Obrelix/Arduino-Granular-Synth-Theremin-v2/Images/IMG_20230304_175001.jpg

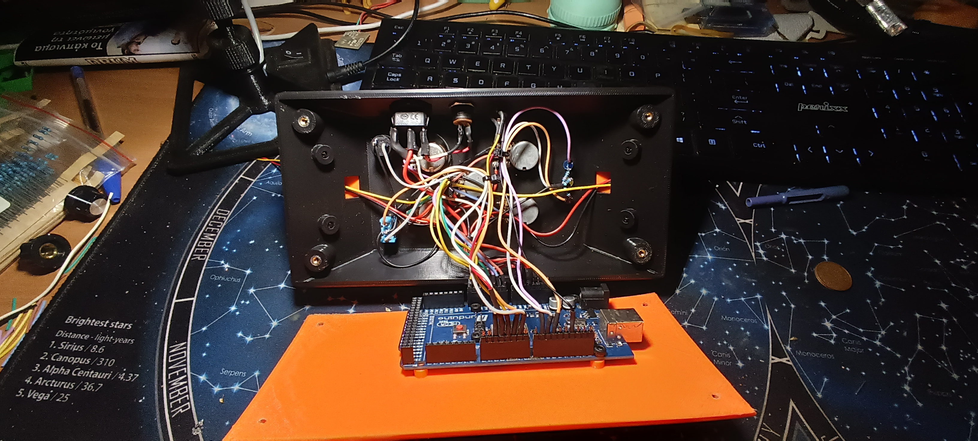
Images/IMG_20230304_175001.jpg
