Obrelix/Arduino-Granular-Synth-Theremin-v2/Images/IMG_20230304_175529.jpg

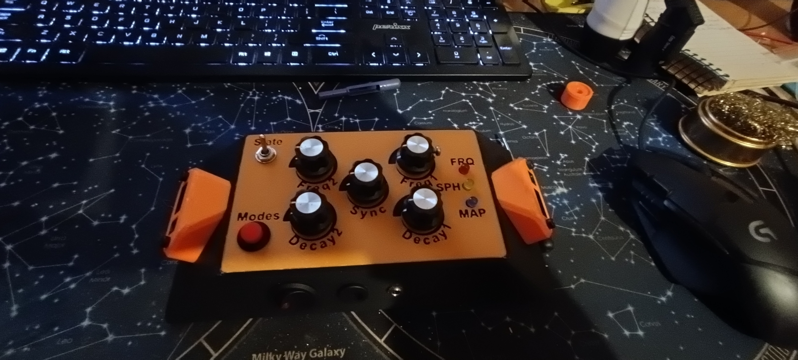
Images/IMG_20230304_175529.jpg
